kevmck451/phase_array_fossn/Circuit_Boards/DE10_Shield/readme.md

# DE10 Shield Circuit Board in KiCad
    - cut board at cut points for each side of DE10 Nano

## Front
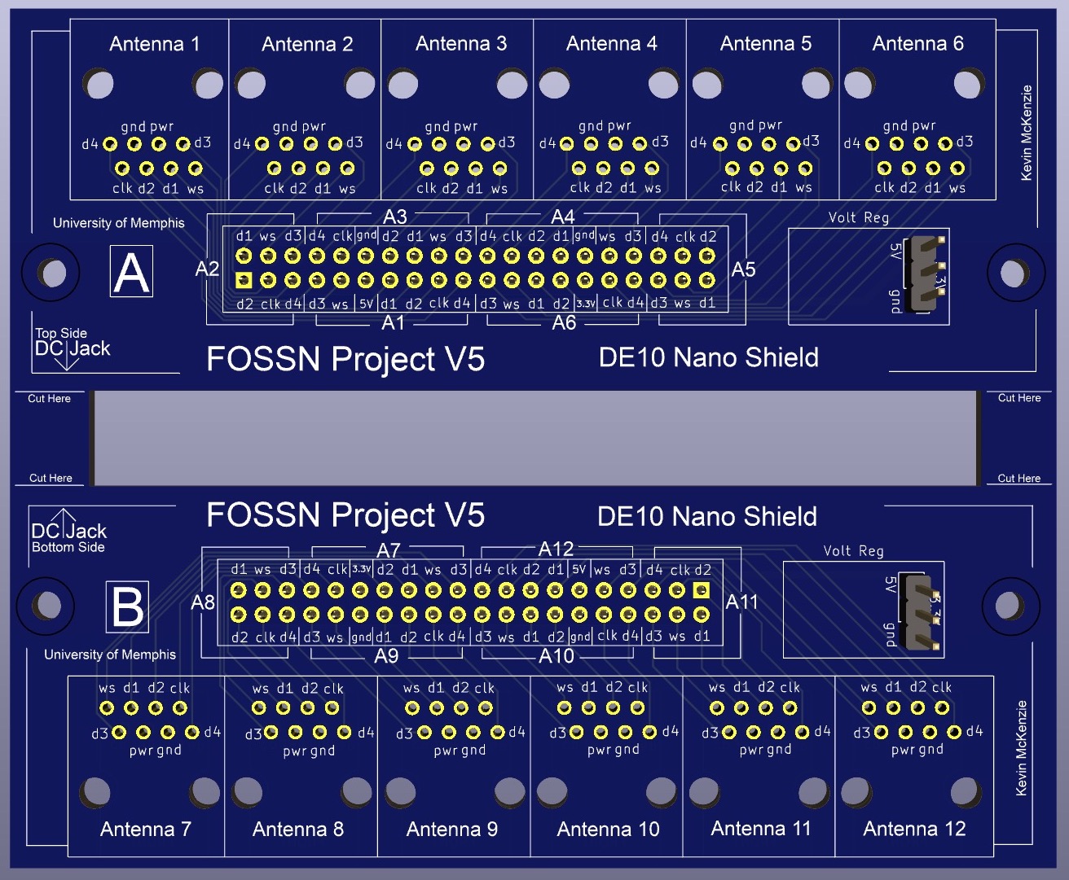
[picture p3: Circuit_Boards/DE10_Shield/shield_front.jpeg]
Sheild Front


## Back
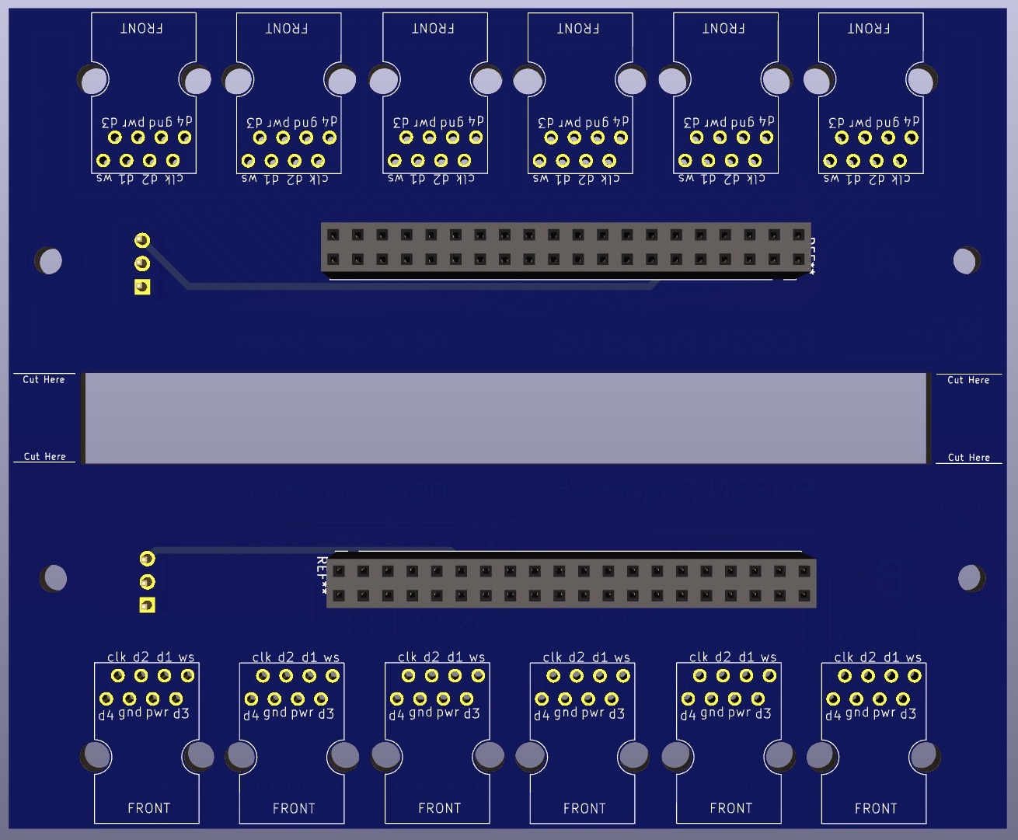
[picture p4: Circuit_Boards/DE10_Shield/shield_back.jpeg]
