kevmck451/phase_array_fossn/Mic_Testing/results 07-08-2024 02-12-56.csv

Channel | Status | RMS | Peak | MicNum | RMS
Ch1 | PASSED | 0.2577 | 0.53281 | 1 | 0.27903
Ch2 | PASSED | 0.27874 | 0.57739 | 2 | 0.18379
Ch3 | PASSED | 0.25935 | 0.53641 | 3 | 0.29007
Ch4 | PASSED | 0.27903 | 0.58661 | 4 | 0.25001
Ch5 | PASSED | 0.3172 | 0.67307 | 5 | 0.29205
Ch6 | FAILED | 0.34542 | 0.71292 | 6 | 0.30534
Ch7 | PASSED | 0.27592 | 0.57278 | 7 | 0.26163
Ch8 | PASSED | 0.27672 | 0.57855 | 8 | 0.27672
Ch9 | FAILED | 0.32335 | 0.67419 | 9 | 0.30184
Ch10 | PASSED | 0.26792 | 0.55283 | 10 | 0.33094
Ch11 | FAILED | 0.32804 | 0.71585 | 11 | 0.2706
Ch12 | PASSED | 0.30752 | 0.65149 | 12 | 0.23714
Ch13 | FAILED | 0.25001 | 0.52005 | 13 | 0.26584
Ch14 | PASSED | 0.30944 | 0.65182 | 14 | 0.29708
Ch15 | FAILED | 0.32657 | 0.67664 | 15 | 0.30182
Ch16 | PASSED | 0.26866 | 0.56451 | 16 | 0.29999
Ch17 | PASSED | 0.29726 | 0.61935 | 17 | 0.31036
Ch18 | PASSED | 0.3095 | 0.68503 | 18 | 0.296
Ch19 | PASSED | 0.25597 | 0.53647 | 19 | 0.32657
Ch20 | FAILED | 0.23714 | 0.51163 | 20 | 0.32408
Ch21 | PASSED | 0.26168 | 0.58502 | 21 | 0.3061
Ch22 | PASSED | 0.31036 | 0.64633 | 22 | 0.2577
Ch23 | PASSED | 0.27541 | 0.57712 | 23 | 0.28809
Ch24 | PASSED | 0.25971 | 0.54706 | 24 | 0.3172
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
