kevmck451/phase_array_fossn/Mic_Testing/results_test1.csv

Channel | Status | RMS | Peak | MicNum
Mic 4 | FAILED | 0.22421 | 0.63846 | 1
Mic 1 | PASSED | 0.27449 | 0.65216 | 2
Mic 3 | FAILED | 0.24069 | 0.52258 | 3
Mic 5 | PASSED | 0.27863 | 0.57193 | 4
Mic 6 | PASSED | 0.28536 | 0.6076 | 5
Mic 6 | PASSED | 0.27868 | 0.5856 | 6
Mic 2 | PASSED | 0.26876 | 0.61987 | 7
Mic 3 | PASSED | 0.29352 | 0.60944 | 8
Mic 5 | FAILED | 0.33212 | 0.70111 | 9
Mic 3 | PASSED | 0.28091 | 0.58881 | 10
Mic 1 | PASSED | 0.27168 | 0.57196 | 11
Mic 3 | FAILED | 0.32259 | 0.77188 | 12
Mic 4 | FAILED | 0.24467 | 0.53015 | 13
Mic 2 | PASSED | 0.28608 | 0.61737 | 14
Mic 5 | FAILED | 0.2484 | 0.51788 | 14
Mic 3 | FAILED | 0.355 | 0.73383 | 16
Mic 5 | PASSED | 0.2847 | 0.65436 | 17
Mic 5 | FAILED | 0.32016 | 0.67023 | 18
Mic 2 | PASSED | 0.28108 | 0.60083 | 20
Mic 4 | FAILED | 0.34016 | 0.70981 | 21
Mic 7 | PASSED | 0.26108 | 0.55832 | 22
Mic 3 | PASSED | 0.27022 | 0.75284 | 23
Mic 8 | FAILED | 0.37688 | 0.78378 | 24
Mic 8 | PASSED | 0.26488 | 0.59198 | 25
Mic 1 | PASSED | 0.26358 | 0.61288 | 26
Mic 4 | PASSED | 0.2697 | 0.55817 | 27
Mic 8 | FAILED | 0.24394 | 0.67627 | 28
Mic 1 | PASSED | 0.25957 | 0.59473 | 29
Mic 6 | PASSED | 0.31312 | 0.64975 | 30
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
